steven-chg/Firefighter-Health-Monitoring-Network/Presentations/Final Demo.pdf

ECE 445 Senior Design Project | Team 17: Firefighter Monitoring Network

# Firefighter Monitoring Network

# ECE 445 Team 17

### Kevin Huang (kuanwei2), Bryan Chang (chchang9), Steven Y M Chang (sychang5)

# LoRa Range Test

# Central Unit Display & Distance From Wearable Unit

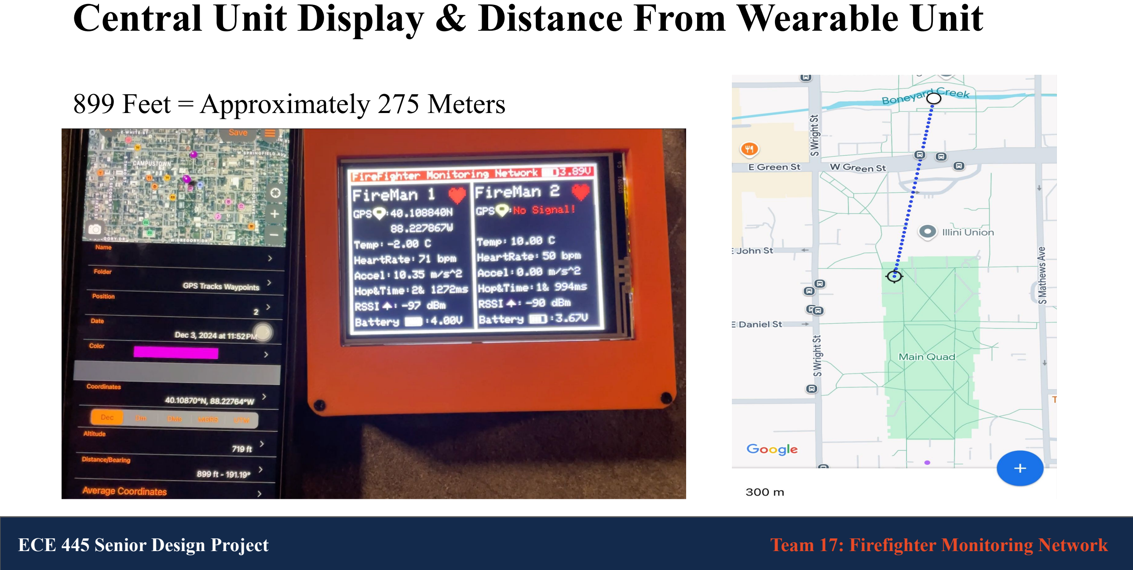
[picture p34: page 3]

## 899 Feet = Approximately 275 Meters

# Battery Life

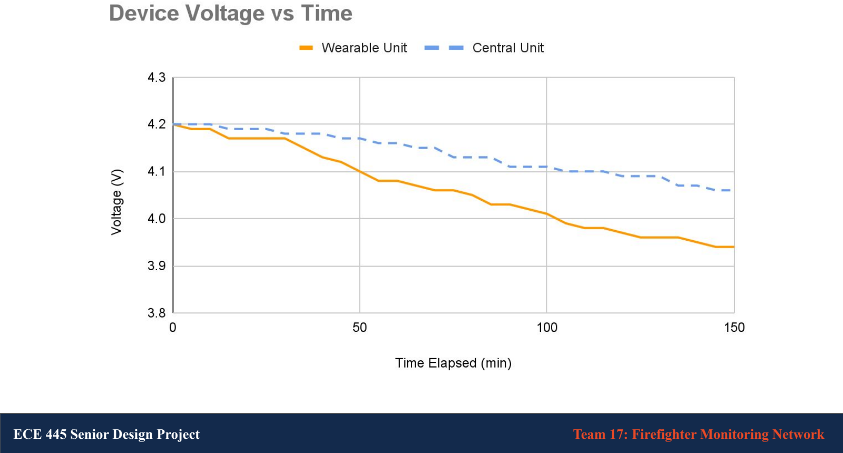
[picture p35: page 5]

# GPS Accuracy Test

# Verification of Wearable Unit Coordinates

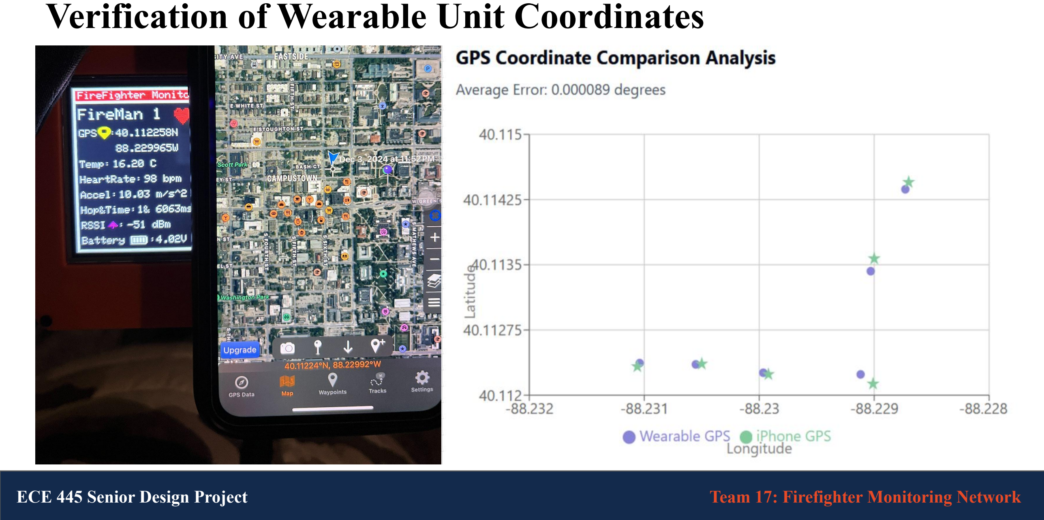
[picture p36: page 7]
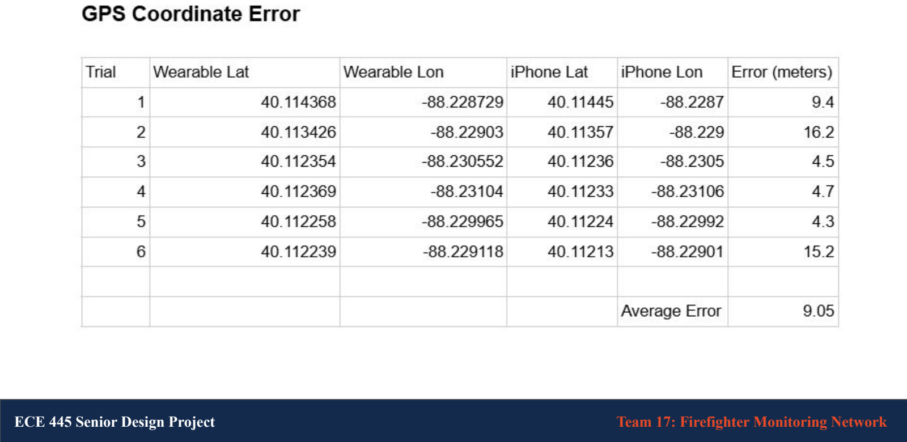
[picture p37: page 8]

# Heartbeat Accuracy Test

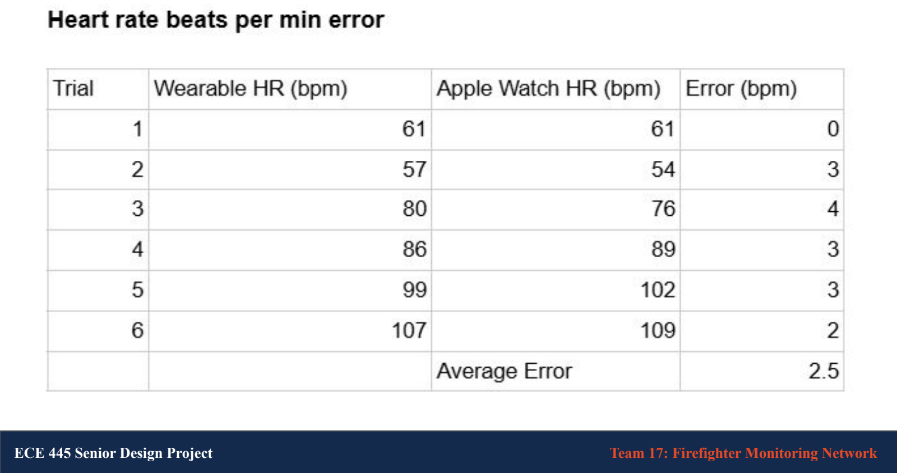
[picture p38: page 10]
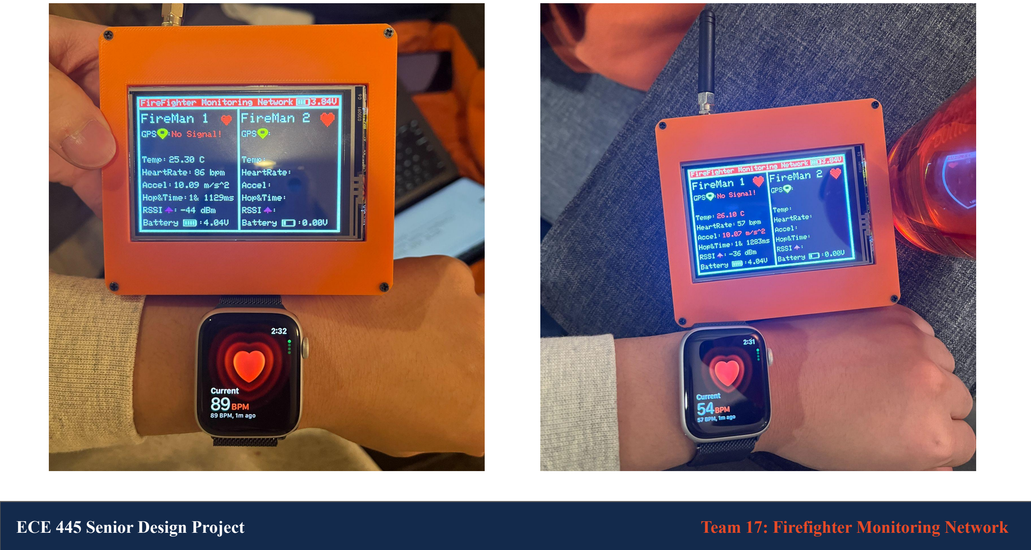
[picture p39: page 11]

# Temperature Accuracy

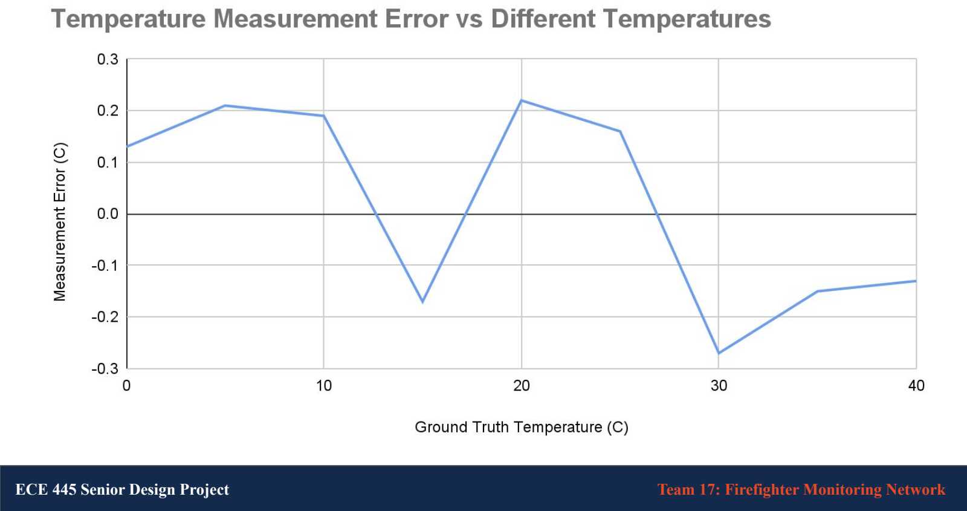
[picture p40: page 13]

# Battery Low Power Alert

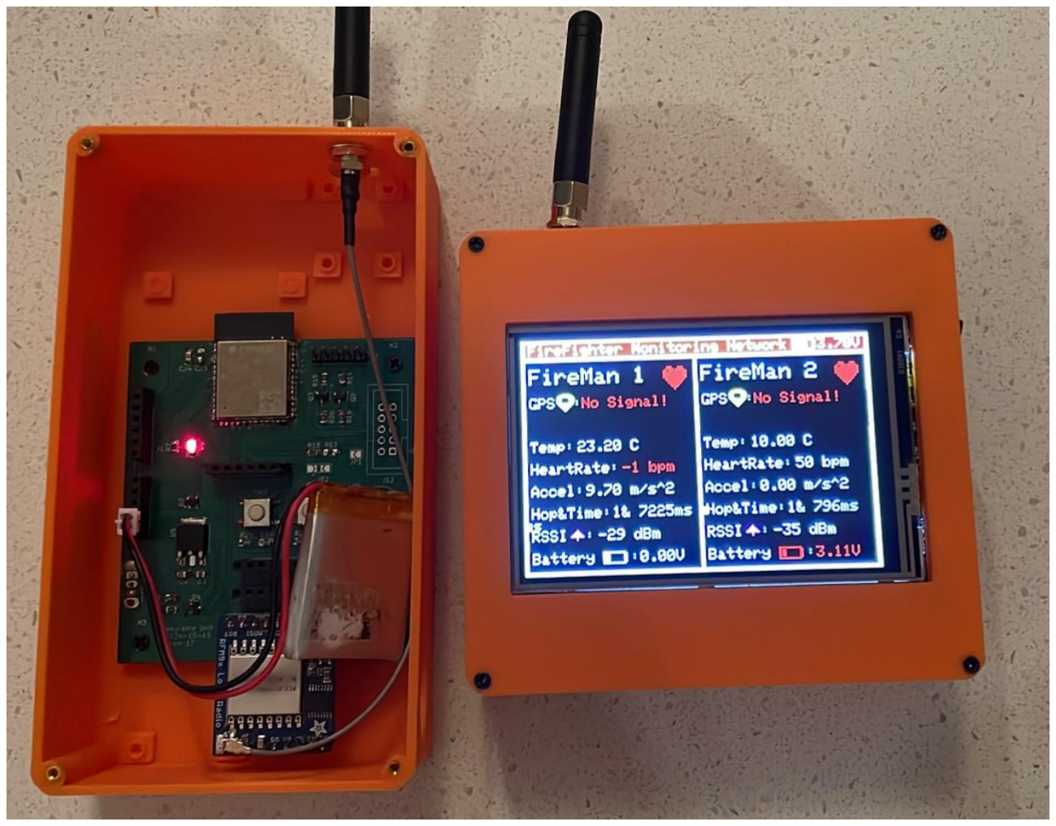
[picture p41: figure]
