steven-chg/Firefighter-Health-Monitoring-Network/Code/Sensors/temperature/temperature.ino

#include <Wire.h>
#include <Adafruit_BMP085.h>
#define seaLevelPressure_hPa 1013.25

Adafruit_BMP085 bmp;
  
void setup() {
  Serial.begin(9600);
  if (!bmp.begin()) {
	Serial.println("Could not find a valid BMP085 sensor, check wiring!");
	while (1) {}
  }
  Serial.println("hi");
}

void loop() {
    Serial.print("Temperature = ");
    Serial.print(bmp.readTemperature());
    Serial.println(" *C");
    
    Serial.print("Pressure = ");
    Serial.print(bmp.readPressure());
    Serial.println(" Pa");

    Serial.print("Altitude = ");
    Serial.print(bmp.readAltitude());
    Serial.println(" meters");

    Serial.print("Pressure at sealevel (calculated) = ");
    Serial.print(bmp.readSealevelPressure());
    Serial.println(" Pa");

    Serial.print("Real altitude = ");
    Serial.print(bmp.readAltitude(seaLevelPressure_hPa * 100));
    Serial.println(" meters");
    
    Serial.println();
    delay(500);
}
